iamakshaymore/meshtalk_t9_communicator/variants/esp32s3/heltec-v4-custom/variant.h

/*
 * CustomUIModule - A T9 Matrix Keypad & Display Driver for Meshtastic
 * Copyright (C) 2026 Akshay Pramod More
 *
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
 * This program is distributed in the hope that it will be useful,
 * but WITHOUT ANY WARRANTY; without even the implied warranty of
 * MERCHANTABILITY or FITNESS FOR A PARTICULAR PURPOSE.  See the
 * GNU General Public License for more details.
 */

#define LED_PIN LED

// Completely disable built-in OLED since we're using custom TFT
// Comment out USE_SSD1306 to disable built-in display initialization
// #define USE_SSD1306 // Disabled - using external ST7789 TFT instead

// Keep the original I2C pins available but don't use for display
#define I2C_SDA SDA_OLED 
#define I2C_SCL SCL_OLED

// Disable primary I2C bus to prevent scanning on GPIO 3/4 (used for keypad)
// #define I2C_SDA1 SDA     // Commented out to disable I2C scanning on port 1
// #define I2C_SCL1 SCL     // Commented out to disable I2C scanning on port 1

#define VEXT_ENABLE 36 // active low, powers the oled display and the lora antenna boost
#define VEXT_ALWAYS_ON // CRITICAL: Keep VEXT powered - only powers GC1109 LDO (no display). Turning off breaks RX!
#define BUTTON_PIN 0

#define ADC_CTRL 37
#define ADC_CTRL_ENABLED HIGH
#define BATTERY_PIN 1 // A battery voltage measurement pin, voltage divider connected here to measure battery voltage
#define ADC_CHANNEL ADC_CHANNEL_0
#define ADC_ATTENUATION ADC_ATTEN_DB_2_5 // lower dB for high resistance voltage divider
#define ADC_MULTIPLIER 4.9 * 1.045

#define USE_SX1262

#define LORA_DIO0 -1 // a No connect on the SX1262 module
#define LORA_RESET 12
#define LORA_DIO1 14 // SX1262 IRQ
#define LORA_DIO2 13 // SX1262 BUSY
#define LORA_DIO3    // Not connected on PCB, but internally on the TTGO SX1262, if DIO3 is high the TXCO is enabled

#define LORA_SCK 9
#define LORA_MISO 11
#define LORA_MOSI 10
#define LORA_CS 8

#define SX126X_CS LORA_CS
#define SX126X_DIO1 LORA_DIO1
#define SX126X_BUSY LORA_DIO2
#define SX126X_RESET LORA_RESET

#define SX126X_DIO2_AS_RF_SWITCH
#define SX126X_DIO3_TCXO_VOLTAGE 1.8

#define USE_GC1109_PA   // We have a GC1109 power amplifier+attenuator
#define LORA_PA_POWER 7 // power en
#define LORA_PA_EN 2   // Changed from GPIO 2 to GPIO 21 (was OLED reset, now unused)
#define LORA_PA_TX_EN 46 // enable tx

//#define HAS_32768HZ 1

// Define our variant name for conditional compilation
#define VARIANT_heltec_v4_custom 1
#define HELTEC_V4_CUSTOM 1

// Force disable any screen-related modules that might interfere
#define HAS_SCREEN 0
