iamakshaymore/meshtalk_t9_communicator/src/modules/CustomUI/init/InitKeypad.cpp

#include "InitKeypad.h"
#include <Keypad.h>
#include <Arduino.h>

// Add missing logging
#ifndef LOG_INFO
#define LOG_INFO(format, ...) Serial.printf("[INFO] " format "\n", ##__VA_ARGS__)
#endif

// Static keypad configuration (horizontally mirrored)
char InitKeypad::keys[InitKeypad::ROWS][InitKeypad::COLS] = {
    {'D', '#', '0', '*'},
    {'C', '9', '8', '7'},
    {'B', '6', '5', '4'},
    {'A', '3', '2', '1'}
};

// Keypad pins - conditional for V3, V4, and MESHTALK_T9 variants
#if defined(VARIANT_heltec_v4_custom)
    // Heltec V4 Custom keypad matrix pins (I2C disabled, USB pins avoided)
    byte InitKeypad::rowPins[InitKeypad::ROWS] = {42, 39, 17, 18};     // KEY_R1, KEY_R2, KEY_R3, KEY_R4 (I2C disabled in variant.h)
    byte InitKeypad::colPins[InitKeypad::COLS] = {41, 40, 48, 47};  // KEY_C1, KEY_C2, KEY_C3, KEY_C4 (avoiding USB pins 19/20)
#elif defined(MESHTALK_T9)
    // MeshTalk T9 keypad matrix pins (4×4 matrix)
    byte InitKeypad::rowPins[InitKeypad::ROWS] = {41, 40, 39, 38};  // reversed
    byte InitKeypad::colPins[InitKeypad::COLS] = {42, 2, 1, 48};    // reversed
#else
    // Heltec V3 Custom keypad matrix pins (default)
    byte InitKeypad::rowPins[InitKeypad::ROWS] = {26, 21, 20, 19};
    byte InitKeypad::colPins[InitKeypad::COLS] = {48, 47, 33, 34};
#endif

// byte InitKeypad::rowPins[InitKeypad::ROWS] = {48, 47, 33, 34};
// byte InitKeypad::colPins[InitKeypad::COLS] = {26, 21, 20, 19};

InitKeypad::InitKeypad() 
    : keypad(nullptr), 
      initialized(false) {
    LOG_INFO("🔧 InitKeypad: Constructor");
}

InitKeypad::~InitKeypad() {
    cleanup();
}

bool InitKeypad::init() {
    LOG_INFO("🔧 InitKeypad: Initializing 4x4 matrix keypad...");
    
    // Create keypad instance
    keypad = new Keypad(makeKeymap(keys), rowPins, colPins, ROWS, COLS);
    keypad->setDebounceTime(50); // 50ms debounce
    
    initialized = true;
    LOG_INFO("🔧 InitKeypad: Keypad initialized with 50ms debounce");
    return true;
}

void InitKeypad::cleanup() {
    LOG_INFO("🔧 InitKeypad: Cleaning up keypad...");
    
    if (keypad) {
        // Safe cleanup without virtual destructor warning
        keypad = nullptr; // Just nullify pointer, let destructor handle cleanup
        initialized = false;
        LOG_INFO("🔧 InitKeypad: Keypad cleaned up");
    }
}
